JoTaijiquan/RV8/Old_Design/RV8/doc/labs/lab6_registers.md

# Lab 6: Register File

## Objective
Build the CPU registers (a0, t0, sp, pg) and connect a0 to the ALU feedback loop.

## Components
| Part | Qty | Description |
|---|:---:|---|
| 74HC574 | 4 | Octal D flip-flop (a0, t0, sp, pg) |
| LED + 330Ω | 8 | a0 output display |

## Concept

```
         ┌──────────────────────────────────┐
         │                                  │
         ▼                                  │
    ┌─────────┐     ┌─────┐     ┌──────┐   │
    │ a0 (U7) │────►│ ALU │────►│result│───┘
    └─────────┘     └─────┘     └──────┘
         ▲               ▲
         │               │
    a0_clk          B input (from IR operand or register)
```

The accumulator (a0) feeds the ALU, and the ALU result writes back to a0.
This creates the compute loop: a0 = a0 OP B.

## Schematic

```
U7 (a0):
  D[7:0] ← ALU result [7:0]
  CLK ← a0_clk (manual pushbutton for now)
  /OE ← GND
  Q[7:0] → ALU input A + LEDs

U8 (t0):
  D[7:0] ← data bus
  CLK ← t0_clk (manual pushbutton)
  /OE ← GND
  Q[7:0] → (available as ALU input B via mux, later)

U9 (sp):
  D[7:0] ← data bus
  CLK ← sp_clk (manual pushbutton)
  /OE ← GND
  Q[7:0] → stack address (used in Step 7)

U10 (pg):
  D[7:0] ← data bus
  CLK ← pg_clk (manual pushbutton)
  /OE ← GND
  Q[7:0] → page register (used in Step 7)
```

## Simulate First

```bash
cd sim/
iverilog -o lab6 lab6_regs_tb.v && vvp lab6
gtkwave lab6.vcd
```

**What to check in GTKWave:**
- `a0`: starts at $00, becomes $05, $08, $0B, $0A, $00
- `result`: shows ALU output before latch
- Feedback loop: a0 feeds back into ALU input A

---

## Procedure

1. Insert U7–U10 (74HC574). Connect VCC (pin 20) and GND (pin 10).
2. U7 (a0): wire D inputs from ALU result outputs.
3. U7 (a0): wire Q outputs to ALU input A (replace DIP switches from Lab 5).
4. U7 (a0): wire Q outputs to 8 LEDs.
5. U7 CLK: connect to a pushbutton (with pull-down, rising-edge triggers latch).
6. Tie U7 /OE to GND (always outputting).
7. Wire U8, U9, U10 similarly (D from data bus, CLK from individual buttons).
8. Remove DIP switches from ALU input A (now driven by a0).

## Test Procedure

| Test | Action | Expected Result |
|:----:|---|---|
| 1 | Set operand=$05 (on U6 or switches), SUB=0 | ALU shows a0+$05 |
| 2 | Press a0_clk | a0 latches result. LEDs show $05 (0+5) |
| 3 | Press a0_clk again | a0 = $0A (5+5) |
| 4 | Press a0_clk again | a0 = $0F (10+5) |
| 5 | Change operand to $01 | ALU shows a0+1 |
| 6 | Press a0_clk repeatedly | a0 counts: $10, $11, $12... |
| 7 | Set SUB=1, operand=$01 | ALU shows a0-1 |
| 8 | Press a0_clk | a0 decrements |
| 9 | RESET (clear a0) | a0 = $00, LEDs off |

## Checkoff

- [ ] a0 latches ALU result on clock edge
- [ ] Feedback loop works: a0 accumulates (adds repeatedly)
- [ ] SUB mode: a0 decrements correctly
- [ ] Overflow wraps: $FF + $01 = $00
- [ ] RESET clears a0 to $00

## Notes
- This is the core compute loop of the CPU. Every ALU instruction does: a0 = a0 OP operand.
- In the final build, a0_clk is generated by the control unit (not a manual button).
- The other registers (t0, sp, pg) are loaded from the data bus, not from the ALU.
- t0 is used as a second operand source: `ADD t0` means a0 = a0 + t0.

## Thai Version

---

# แลป 6: Register File (ชุดรีจิสเตอร์)

---

## เป้าหมาย

สร้าง register a0 (accumulator) และต่อเข้ากับ ALU เป็นวงรอบ — ให้ CPU คำนวณซ้ำได้

---

## ความรู้พื้นฐาน

**Accumulator (a0)** = ตัวเก็บผลลัพธ์หลัก ทุกการคำนวณจะเป็น: a0 = a0 OP ค่าอะไรสักอย่าง

**วงรอบคำนวณ:**
```
a0 ──► ALU ──► ผลลัพธ์ ──► กลับเข้า a0
```
ทุกครั้งที่กด clock ผลลัพธ์ใหม่จะถูกเก็บใน a0

**ตัวอย่าง:** ถ้า operand = 5 และกด clock 3 ครั้ง:
- ครั้งที่ 1: a0 = 0 + 5 = 5
- ครั้งที่ 2: a0 = 5 + 5 = 10
- ครั้งที่ 3: a0 = 10 + 5 = 15

---

## อุปกรณ์

| อุปกรณ์ | จำนวน | ทำหน้าที่อะไร |
|---|:---:|---|
| 74HC574 | 4 | register a0, t0, sp, pg |
| LED + 330Ω | 8 | แสดงค่า a0 |

---

## ผังวงจร

```
         ┌──────────────────────────────┐
         │                              │
         ▼                              │
    ┌─────────┐     ┌─────┐     ┌──────┴──┐
    │ a0 (U7) │────►│ ALU │────►│ผลลัพธ์   │
    │         │     └─────┘     └─────────┘
    └─────────┘          ▲
         │               │
       LED 8 ดวง    B input (จาก operand)
```

---

## ขั้นตอนต่อวงจร

1. เสียบ U7–U10 (74HC574) ต่อ VCC (pin 20) และ GND (pin 10)
2. U7 (a0): ต่อ D จาก ALU result
3. U7 (a0): ต่อ Q ไปที่ ALU input A (แทน DIP switch จาก Lab 5)
4. U7 (a0): ต่อ Q ไปที่ LED 8 ดวง
5. U7 CLK: ต่อกับปุ่มกด (กดแล้ว a0 จะเก็บค่าใหม่)
6. ต่อ /OE → GND (เปิดตลอด)
7. ถอด DIP switch ออกจาก ALU input A (ตอนนี้ a0 ขับแทน)

---

## ทดสอบ

| ขั้น | ทำอะไร | ผลที่ถูกต้อง |
|:----:|---|---|
| 1 | ตั้ง operand = $05, SUB = 0 | ALU แสดง a0 + 5 |
| 2 | กดปุ่ม a0_clk | LED แสดง $05 (0+5) |
| 3 | กดปุ่ม a0_clk อีก | LED แสดง $0A (5+5) |
| 4 | กดปุ่ม a0_clk อีก | LED แสดง $0F (10+5) |
| 5 | เปลี่ยน operand = $01 | ALU แสดง a0 + 1 |
| 6 | กดปุ่มหลายครั้ง | a0 นับขึ้น: $10, $11, $12... |
| 7 | เปลี่ยน SUB = 1, operand = $01 | ALU แสดง a0 - 1 |
| 8 | กดปุ่ม | a0 นับลง |
| 9 | กด RESET | a0 = $00, LED ดับหมด |

---

## เช็คลิสต์ผ่าน

- [ ] a0 เก็บผลลัพธ์จาก ALU เมื่อกด clock
- [ ] วงรอบทำงาน: กดซ้ำแล้ว a0 สะสมค่า
- [ ] ลบทำงาน: a0 ลดลงถูกต้อง
- [ ] ล้น: $FF + $01 = $00 (วนกลับ)
- [ ] RESET ทำให้ a0 = $00

---

## จำลองก่อนต่อจริง

```bash
cd sim/
iverilog -o lab6 lab6_regs_tb.v && vvp lab6
gtkwave lab6.vcd
```

---

## หมายเหตุ

- นี่คือ "หัวใจของการคำนวณ" — ทุกคำสั่ง ALU ทำ: a0 = a0 OP operand
- ใน CPU จริง a0_clk มาจาก Control Unit (ไม่ใช่ปุ่มกด)
- register อื่น (t0, sp, pg) โหลดจาก Data Bus ไม่ใช่จาก ALU
- Lab ถัดไป (Lab 7) จะเพิ่ม pointer และ RAM access
