JoTaijiquan/RV8/Old_Design/RV8/doc/diagrams/rv8_cpu_ttl_chip_level_schematic.pdf

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

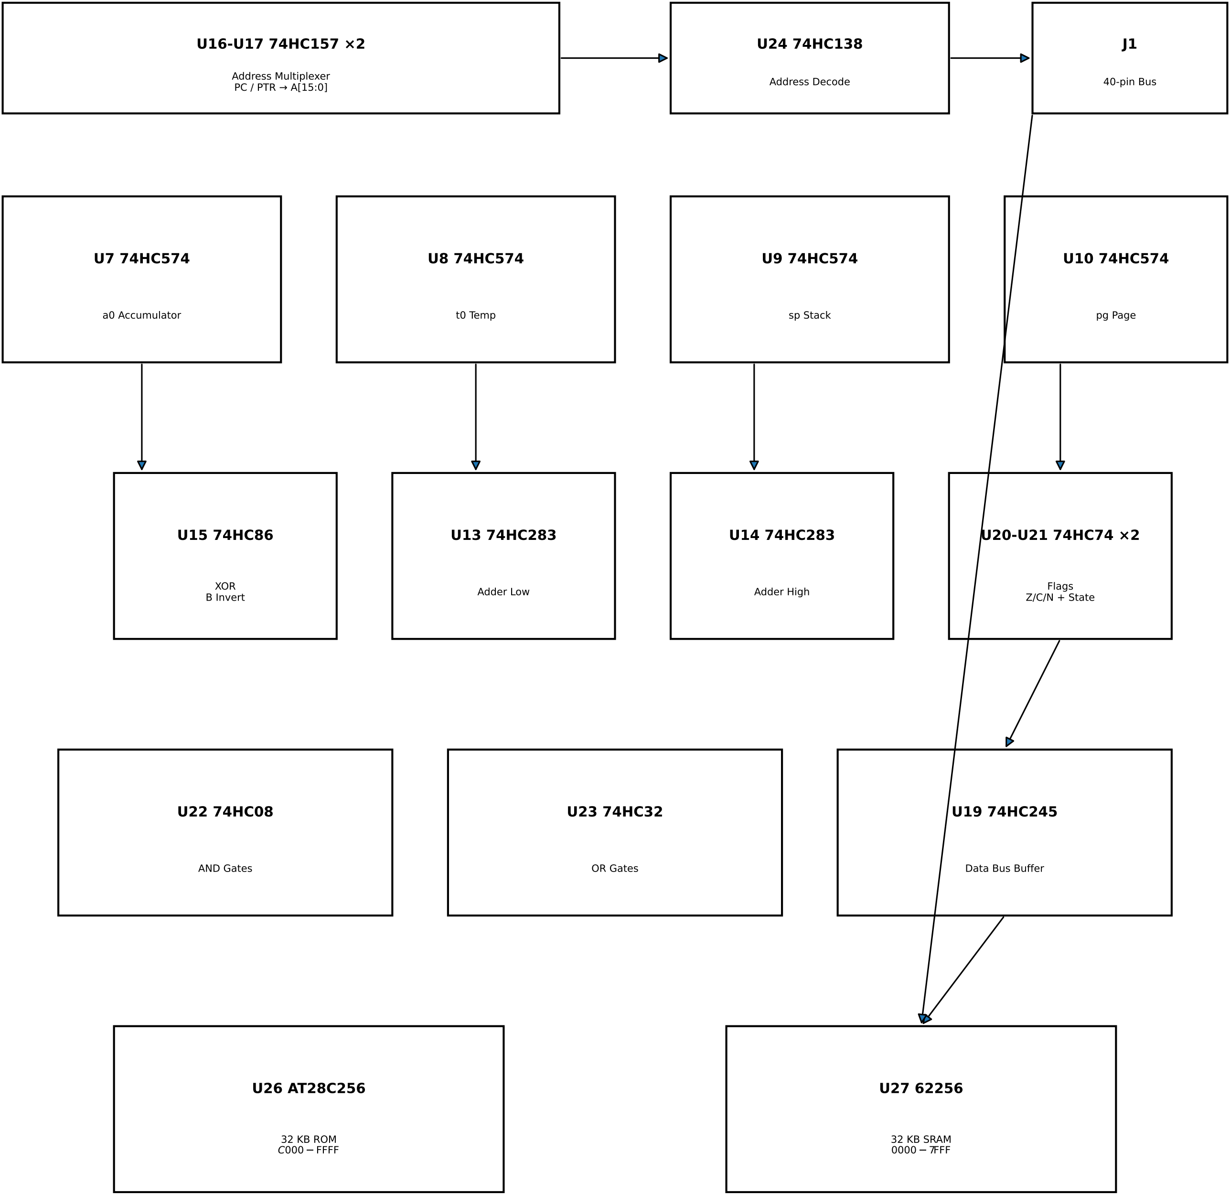
[picture p1: figure]
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
